dpiegdon/wurstradar/hardware/ltspice/wurstradar.asc

C1: cap; 1µ
C2: cap; 1µ
R1: res; 1200
R2: res; 8800
R3: res; 1000
R4: res; 3500
R5: res; 4700
R6: res; 4700
U2: AD823
V1: voltage; 3.3
V2: voltage; SINE(0 0.3 100000)
Named nets: 0
.tran 0.02
